yhnx/Power-Supply/EN2091_AnalogProject_PowerSupply/DM_27/testing.asc

16vC2: cap; 10µ
16vC4: cap; 10µ
50vC3: polcap; 2.2µ
63vC2: polcap; 10µ
C1: polcap; 2200µ
C5: polcap; 2200µ
D1: diode; 1N4007
D2: diode; 1N4007
D3: diode; 1N4007
D4: diode; 1N4007
D5: zener; CDZV24B
L1: ind2; 75
L2: ind2; 1
load: res; 200
Q1: npn; 2N3055
Q2: npn; 2N3904
R1: res; 720
R2: res; 404
R3: res; 216
R4: res; 0.47
R5: res; 1
R6: res; 0.47
U1: LT1085
V1: voltage; SINE(0 325 50); AC 325 0
var_R: res; 10k
Named nets: 0
.tran 0 10s 0 0.1s uic
K L1 L2 0.99
